mmastrac/gpsclock/fontmaker/display/A1.png

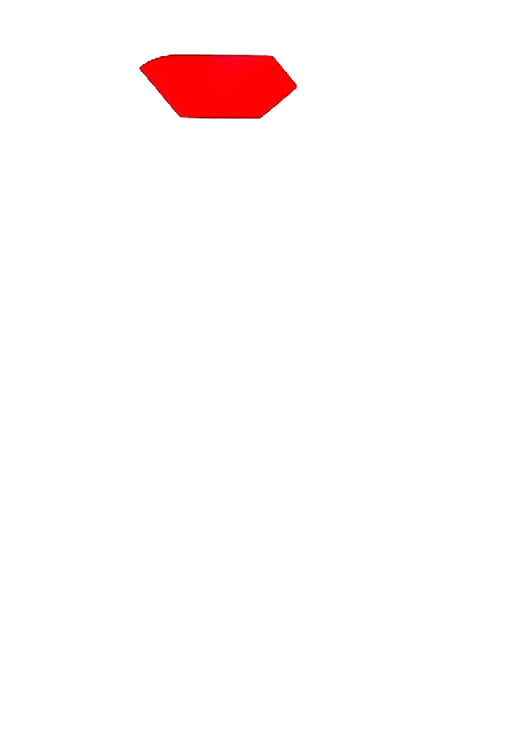
fontmaker/display/A1.png
