mmastrac/gpsclock/fontmaker/display/B.png

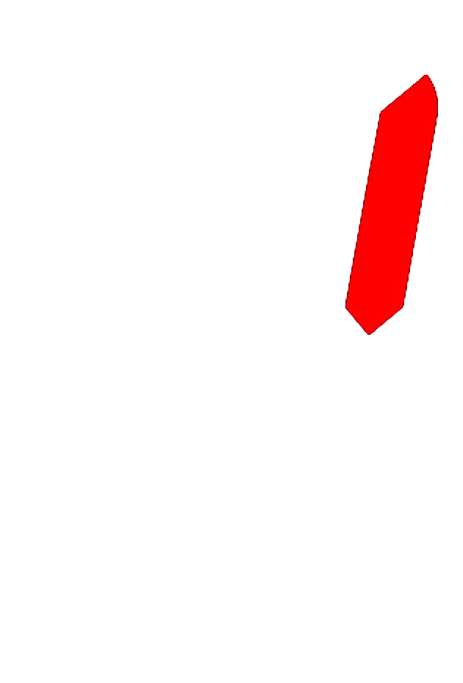
fontmaker/display/B.png
