mmastrac/gpsclock/fontmaker/display/background.png

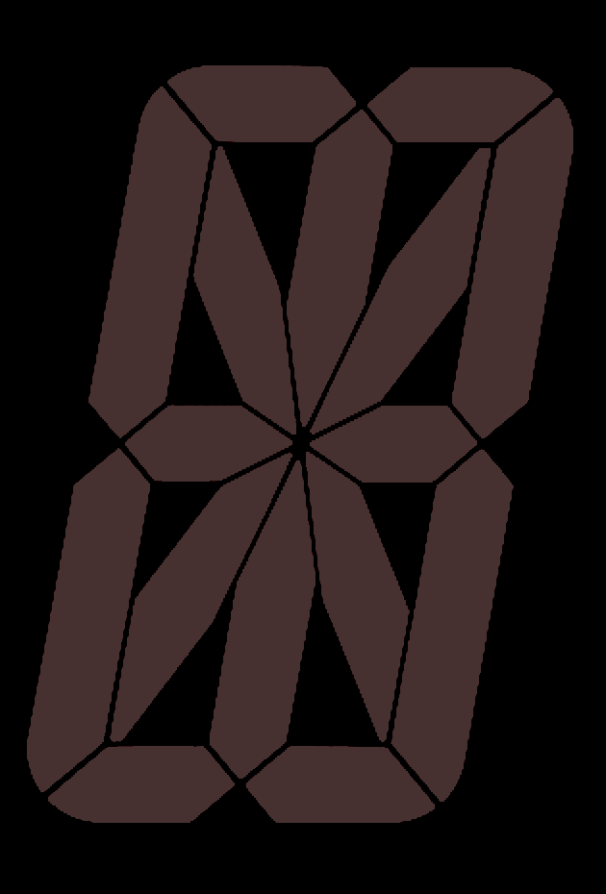
fontmaker/display/background.png
