mmastrac/gpsclock/fontmaker/display/C.png

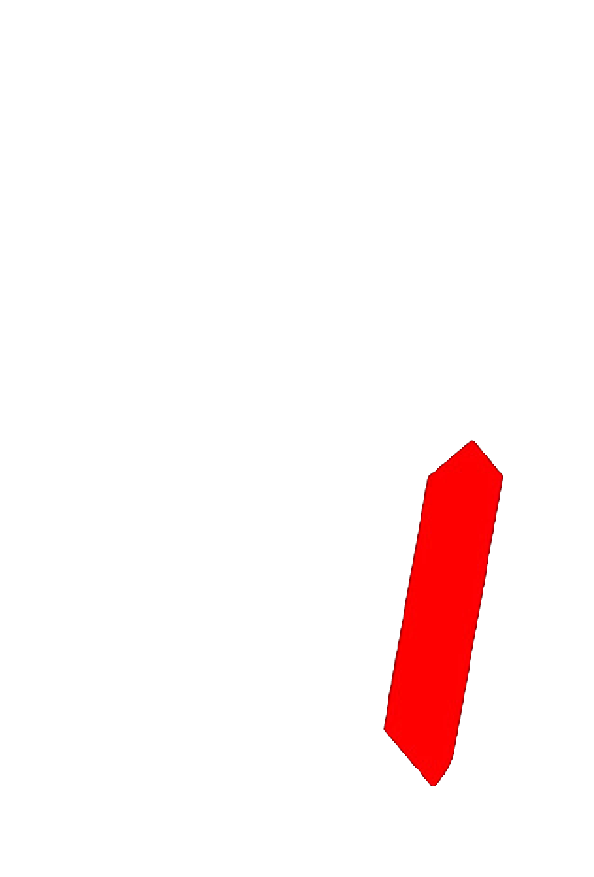
fontmaker/display/C.png
