mmastrac/gpsclock/fontmaker/display/F.png

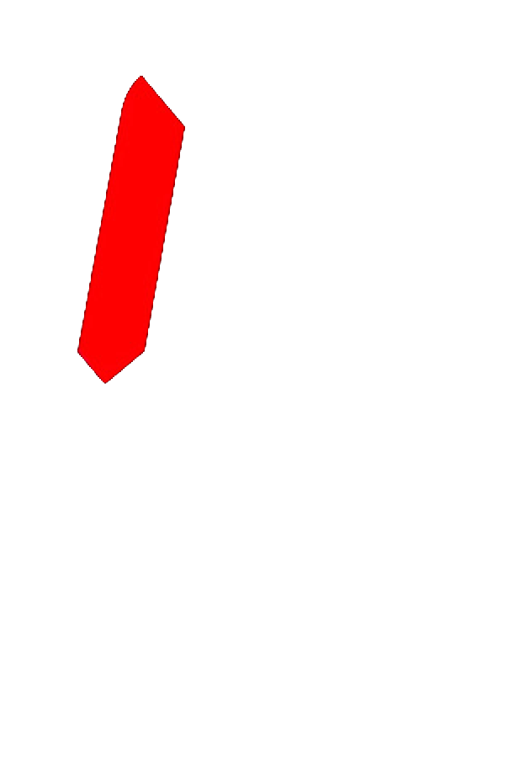
fontmaker/display/F.png
