mmastrac/gpsclock/fontmaker/display/G1.png

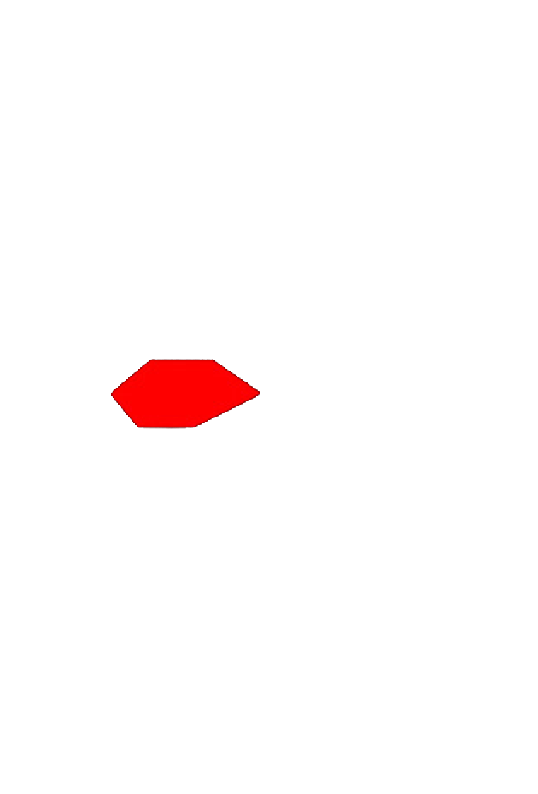
fontmaker/display/G1.png
