mmastrac/gpsclock/fontmaker/display/G2.png

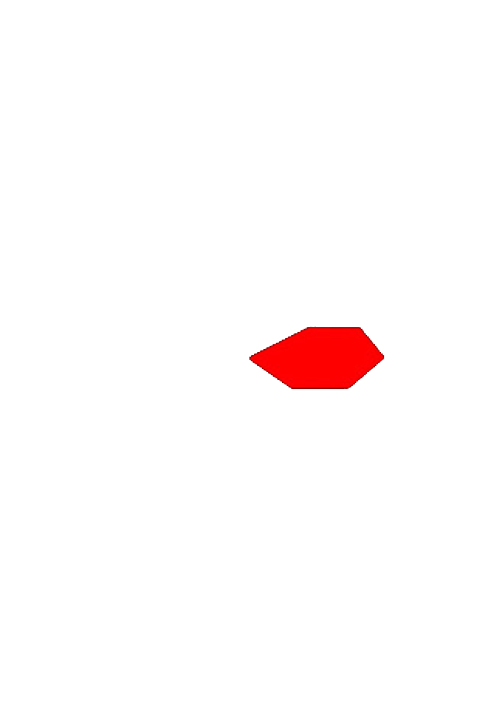
fontmaker/display/G2.png
