mmastrac/gpsclock/fontmaker/display/H.png

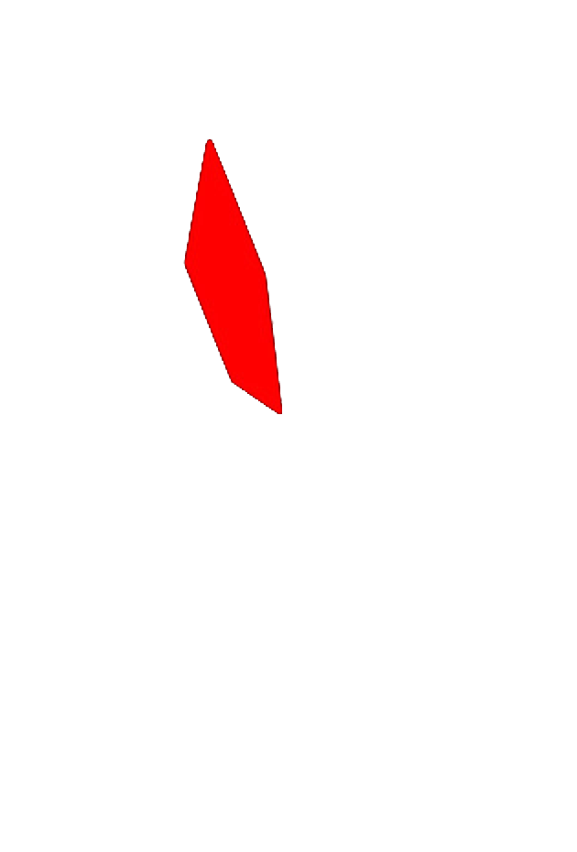
fontmaker/display/H.png
