mmastrac/gpsclock/fontmaker/display/J.png

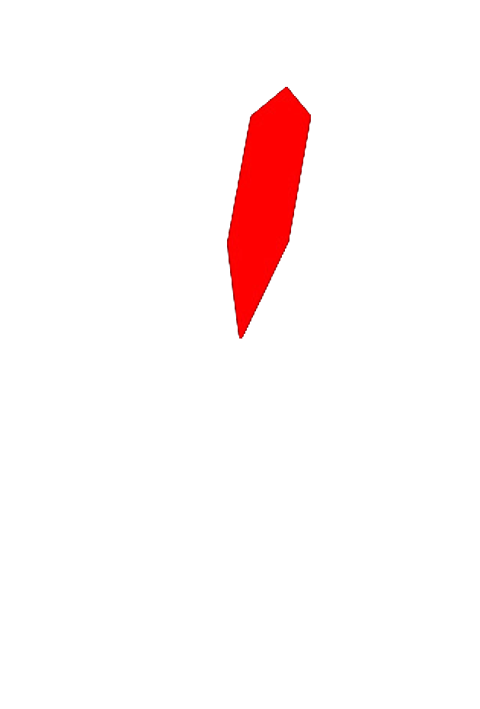
fontmaker/display/J.png
