mmastrac/gpsclock/fontmaker/display/L.png

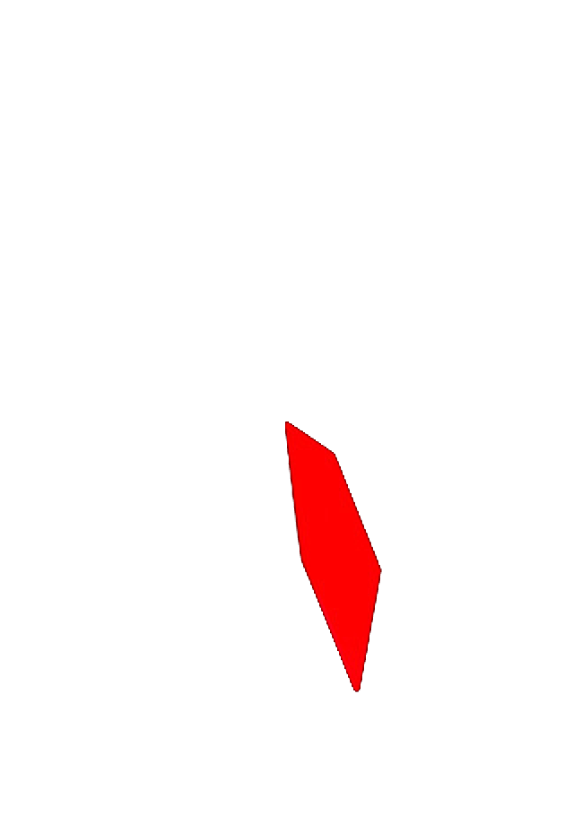
fontmaker/display/L.png
