mmastrac/gpsclock/fontmaker/display/N.png

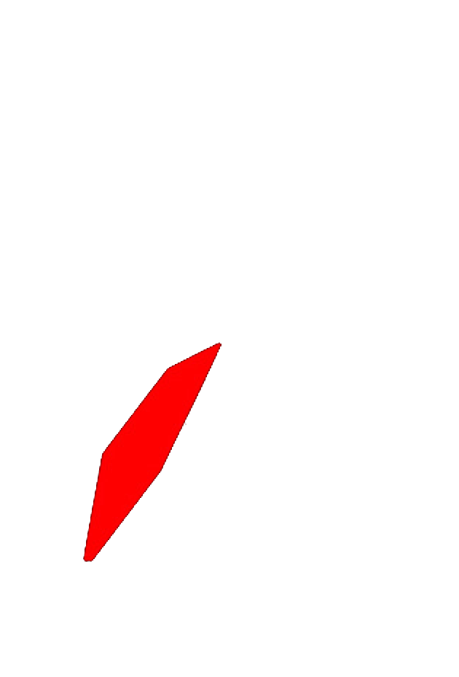
fontmaker/display/N.png
