mmastrac/gpsclock/displaydriver/serial.c

#include <avr/interrupt.h>
#include <avr/io.h>
#include <avr/cpufunc.h>
#include <string.h>
#include <stdbool.h>
#include "serial.h"
#include "bitbang.h"
#include "pins.h"
#include "calibrate_serial.h"
#include "serial_timing.h"

// Serial 

#define SERIAL_SIZE 32

// Input/output buffer
typedef struct serial_buffer_t {
	uint8_t uart_start;
	volatile uint8_t uart_end;
	volatile uint8_t uart_buffer[SERIAL_SIZE];
} serial_buffer_t;

// The serial value we are clocking in
uint8_t receive_value = 0;
uint8_t receive_counter = 0;
uint8_t send_value = 0;
uint8_t send_counter = 0;

serial_buffer_t uart_input = { 0 };
serial_buffer_t uart_output = { 0 };

inline void _serial_push(serial_buffer_t* uart, uint8_t value);
uint8_t _serial_available(serial_buffer_t* buffer);
uint8_t _serial_read(serial_buffer_t* buffer);
void _serial_push(serial_buffer_t* buffer, uint8_t value);
inline void receive_check();
inline void receive_bit();
inline void send_bit();

typedef enum receive_flag_t { RECEIVE_IDLE = -1, RECEIVE_A = 0, RECEIVE_B = 1, RECEIVE_C = 2, RECEIVE_D = 3 } receive_flag_t;
typedef enum send_flag_t { SEND_IDLE = 0, SEND_ACTIVE = 1 } send_flag_t;
typedef enum serial_timer_state_t { A = 0, B = 1, C = 2, D = 3 } serial_timer_state_t;

receive_flag_t receive_flag = RECEIVE_IDLE;
send_flag_t send_flag = SEND_IDLE;
serial_timer_state_t serial_timer_state = A;

ISR(TIMER0_COMPA_vect) {
	receive_check();

	if (serial_timer_state == A) {
		// Sending is always in phase A
		send_bit();
	}

	serial_timer_state = (serial_timer_state + 1) & 3;
}

void send_bit() {
	if (send_flag == SEND_IDLE) {
		if (_serial_available(&uart_output)) {
			send_flag = SEND_ACTIVE;
			send_counter = 0;
			send_value = _serial_read(&uart_output);
		}
	}

	if (send_flag == SEND_ACTIVE) {
		switch (send_counter) {
			case 0:
				// Start
				setLow(DATAOUT);
				break;
			case 1:
			case 2:
			case 3:
			case 4:
			case 5:
			case 6:
			case 7:
			case 8:
				setState(DATAOUT, send_value & (1 << (send_counter - 1)));
				break;
			case 9:
				// Stop bit
				setHigh(DATAOUT);
				send_flag = SEND_IDLE;
				break;
		}

		send_counter++;
	}
}

void receive_check() {
	if (receive_flag == RECEIVE_IDLE) {
		uint8_t pin_state = readState(DATAIN);
		if (pin_state == 0) {
			// OK, time to start receiving, but in the next phase so we can ensure 
			// good signal read quality
			receive_flag = (serial_timer_state + 1) & 3;
			receive_value = 0;
			receive_counter = 0;
		}
	}

	if (receive_flag == (receive_flag_t)serial_timer_state) {
		receive_bit();
	}
}

void receive_bit() {
	switch (receive_counter) {
		case 0:
			// Start bit (zero)
			if (readState(DATAIN)) {
				_serial_push(&uart_input, 0xEE);
				// Spurious pin change
				receive_flag = RECEIVE_IDLE;			
			}
			break;
		case 1:
		case 2:
		case 3:
		case 4:
		case 5:
		case 6:
		case 7:
		case 8:
			// Clock in the serial bit
			receive_value |= (readState(DATAIN) ? 1 : 0) << (receive_counter - 1);
			break;
		case 9:
			// Stop bit (one)
			if (readState(DATAIN)) {
				_serial_push(&uart_input, receive_value);				
			}

			receive_flag = RECEIVE_IDLE;
			break;
	}

	receive_counter++;
}

void _serial_push(serial_buffer_t* buffer, uint8_t value) {
	buffer->uart_buffer[buffer->uart_end] = value;
	buffer->uart_end++;
	if (buffer->uart_end >= SERIAL_SIZE)
		buffer->uart_end = 0;
}

uint8_t _serial_available(serial_buffer_t* buffer) {
	// Read volatile end once
	uint8_t end = buffer->uart_end;

	if (end == buffer->uart_start)
		return 0;

	if (end > buffer->uart_start)
		return end - buffer->uart_start;

	return SERIAL_SIZE - (buffer->uart_start - end);
}

void _serial_drop(serial_buffer_t* buffer, uint8_t count) {
	buffer->uart_start = (buffer->uart_start + count) % SERIAL_SIZE;
}

uint8_t _serial_peek(serial_buffer_t* buffer, uint8_t where) {
	return buffer->uart_buffer[(buffer->uart_start + where) % SERIAL_SIZE];
}

uint8_t _serial_read(serial_buffer_t* buffer) {
	uint8_t ret = buffer->uart_buffer[buffer->uart_start];
	buffer->uart_start++;
	if (buffer->uart_start >= SERIAL_SIZE)
		buffer->uart_start = 0;

	return ret;
}

uint8_t serial_available() {
	return _serial_available(&uart_input);
}

uint8_t serial_read() {
	return _serial_read(&uart_input);
}

uint8_t serial_peek(uint8_t where) {
	return _serial_peek(&uart_input, where);
}

void serial_drop(uint8_t count) {
	_serial_drop(&uart_input, count);
}

void serial_write(uint8_t c) {
	_serial_push(&uart_output, c);
}

void serial_write_buffer(uint8_t* buffer, uint8_t length) {
	for (uint8_t i = 0; i < length; i++) {
		_serial_push(&uart_output, buffer[i]);
	}
}

void serial_write_string(char* buffer) {
	serial_write_buffer((uint8_t*)buffer, strlen(buffer));
}

void initialize_serial() {
	// Serial timer (see comments above)

	// CTC mode, OCRA is top
	TCCR0A = _BV(WGM01);
	
	// Bit-bang serial needs the full timer period
	OCR0A = SERIAL_TIMER_COMPARE;

	// Enable the timer for bit-bang serial
	TCCR0B = SERIAL_CLOCK_DIVISOR;

	calibrate_serial();

	// Timer interrupts for 1/4 of each serial bit
	OCR0A = SERIAL_TIMER_COMPARE_QUARTER;

	// Enable timer interrupts -- compareA for timer0 and overflow for timer1
	TCNT0 = 0;
	setBit(TIMSK, OCIE0A);
}
