mmastrac/gpsclock/displaydriver/sin_cycle.c

#include <avr/pgmspace.h>
#include "sin_cycle.h"

// [int(4095 / 2.0 * (math.sin(2 * math.pi * (x / 1024.0)) + 1)) for x in range(0,1024)]
const uint16_t SIN_CYCLE[1024] PROGMEM = {
	2047, 2060, 2072, 2085, 2097, 2110, 2122, 2135, 2147, 2160, 2173, 2185, 2198, 2210, 2223, 2235, 2248, 2260, 2273, 2285, 2298, 2310, 2323, 2335, 2347, 2360, 2372, 2385, 2397, 2409, 2422, 2434, 2446, 2459, 2471, 2483, 2496, 2508, 2520, 2532, 2545, 2557, 2569, 2581, 2593, 2605, 2617, 2629, 2641, 2653, 2665, 2677, 2689, 2701, 2713, 2725, 2737, 2749, 2760, 2772, 2784, 2796, 2807, 2819, 2831, 2842, 2854, 2865, 2877, 2888, 2900, 2911, 2922, 2934, 2945, 2956, 2968, 2979, 2990, 3001, 3012, 3023, 3034, 3045, 3056, 3067, 3078, 3089, 3100, 3110, 3121, 3132, 3142, 3153, 3164, 3174, 3185, 3195, 3205, 3216, 3226, 3236, 3246, 3257, 3267, 3277, 3287, 3297, 3307, 3317, 3326, 3336, 3346, 3356, 3365, 3375, 3384, 3394, 3403, 3413, 3422, 3431, 3441, 3450, 3459, 3468, 3477, 3486, 3495, 3504, 3512, 3521, 3530, 3539, 3547, 3556, 3564, 3573, 3581, 3589, 3597, 3606, 3614, 3622, 3630, 3638, 3646, 3653, 3661, 3669, 3676, 3684, 3692, 3699, 3706, 3714, 3721, 3728, 3735, 3742, 3749, 3756, 3763, 3770, 3777, 3784, 3790, 3797, 3803, 3810, 3816, 3822, 3829, 3835, 3841, 3847, 3853, 3859, 3864, 3870, 3876, 3881, 3887, 3893, 3898, 3903, 3909, 3914, 3919, 3924, 3929, 3934, 3939, 3943, 3948, 3953, 3957, 3962, 3966, 3971, 3975, 3979, 3983, 3987, 3991, 3995, 3999, 4003, 4006, 4010, 4013, 4017, 4020, 4024, 4027, 4030, 4033, 4036, 4039, 4042, 4045, 4047, 4050, 4053, 4055, 4058, 4060, 4062, 4064, 4066, 4068, 4070, 4072, 4074, 4076, 4078, 4079, 4081, 4082, 4083, 4085, 4086, 4087, 4088, 4089, 4090, 4091, 4091, 4092, 4093,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
};

uint16_t sin_cycle(uint16_t cycle) {
	return pgm_read_word(&SIN_CYCLE[cycle]);
}
